Timoute/EVE_2023-2024_Project/Core/Inc/mpu6050.h

#ifndef INC_GY521_H_
#define INC_GY521_H_

#endif /* INC_GY521_H_ */

#include <stdint.h>
#include "i2c.h"

// MPU6050 structure
typedef struct
{

    int16_t Accel_X_RAW;
    int16_t Accel_Y_RAW;
    int16_t Accel_Z_RAW;
    double Ax;
    double Ay;
    double Az;

    int16_t Gyro_X_RAW;
    int16_t Gyro_Y_RAW;
    int16_t Gyro_Z_RAW;
    double Gx;
    double Gy;
    double Gz;

    float Temperature;

    double KalmanAngleX;
    double KalmanAngleY;
} MPU6050_t;


// Kalman structure
typedef struct
{
    double Q_angle;
    double Q_bias;
    double R_measure;
    double angle;
    double bias;
    double P[2][2];
} Kalman_t;

static float previousAccelX = 0.0;
static float previousAccelY = 0.0;
static float previousAccelZ = 0.0;

static float velocityX = 0.0;
static float velocityY = 0.0;
static float velocityZ = 0.0;

uint8_t MPU6050_Init(I2C_HandleTypeDef *I2Cx);

void MPU6050_Read_Accel(I2C_HandleTypeDef *I2Cx, MPU6050_t *DataStruct);

void MPU6050_Read_Gyro(I2C_HandleTypeDef *I2Cx, MPU6050_t *DataStruct);

void MPU6050_Read_Temp(I2C_HandleTypeDef *I2Cx, MPU6050_t *DataStruct);

void MPU6050_Read_All(I2C_HandleTypeDef *I2Cx, MPU6050_t *DataStruct);

double Kalman_getAngle(Kalman_t *Kalman, double newAngle, double newRate, double dt);

void calculateVelocities(MPU6050_t *DataStruct);
